capopaul/Jack-Bluetooth-Converter/doc/images_sw/bclk_oscilloscope.TIF

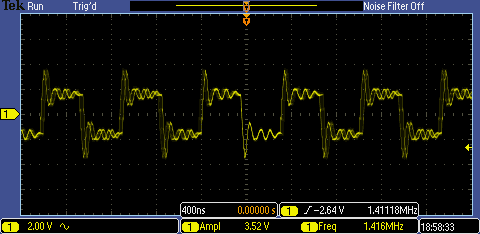
doc/images_sw/bclk_oscilloscope.TIF
