capopaul/Jack-Bluetooth-Converter/doc/images_sw/TEK00001.TIF

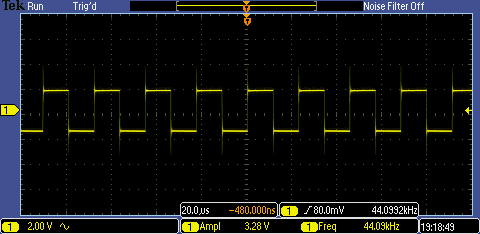
doc/images_sw/TEK00001.TIF
