capopaul/Jack-Bluetooth-Converter/doc/images_sw/TEK00002.TIF

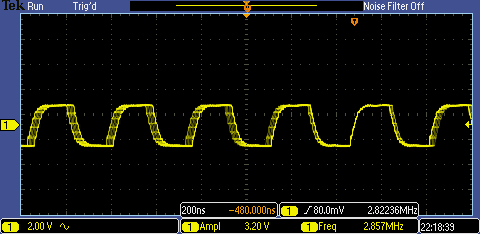
doc/images_sw/TEK00002.TIF
