capopaul/Jack-Bluetooth-Converter/doc/images_sw/TEK00003.TIF

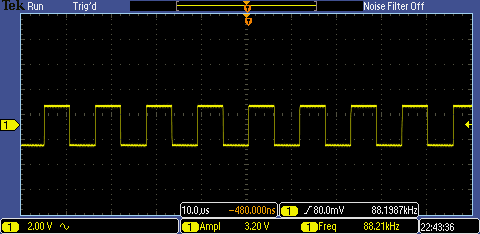
doc/images_sw/TEK00003.TIF
