capopaul/Jack-Bluetooth-Converter/doc/images_sw/TEK00004.TIF

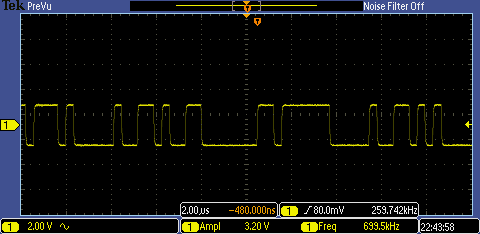
doc/images_sw/TEK00004.TIF
