capopaul/Jack-Bluetooth-Converter/doc/images_sw/TEK00005.TIF

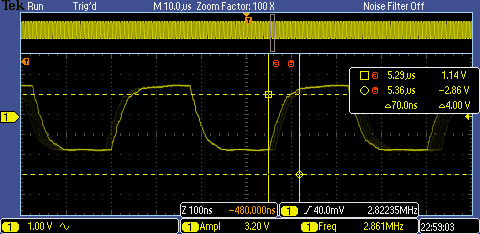
doc/images_sw/TEK00005.TIF
