capopaul/Jack-Bluetooth-Converter/doc/images_assembly/2025-04-11-PC-20250411_151901.jpg

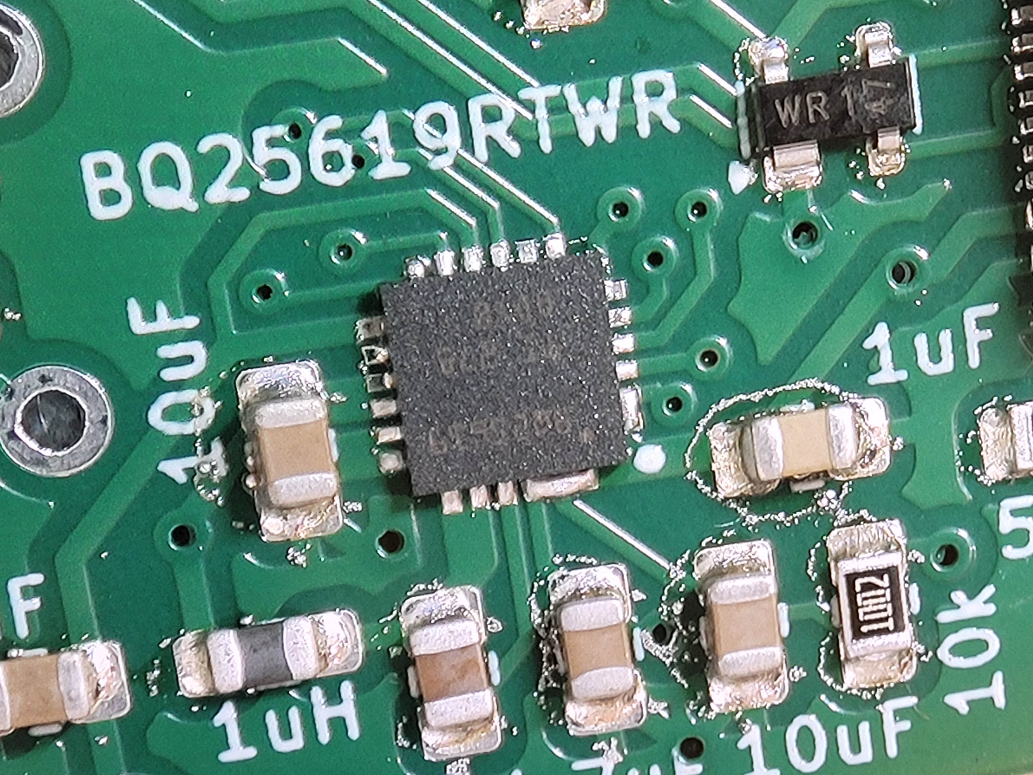
doc/images_assembly/2025-04-11-PC-20250411_151901.jpg
