capopaul/Jack-Bluetooth-Converter/doc/images_assembly/2025-04-20-PC-20250420_151838.jpg

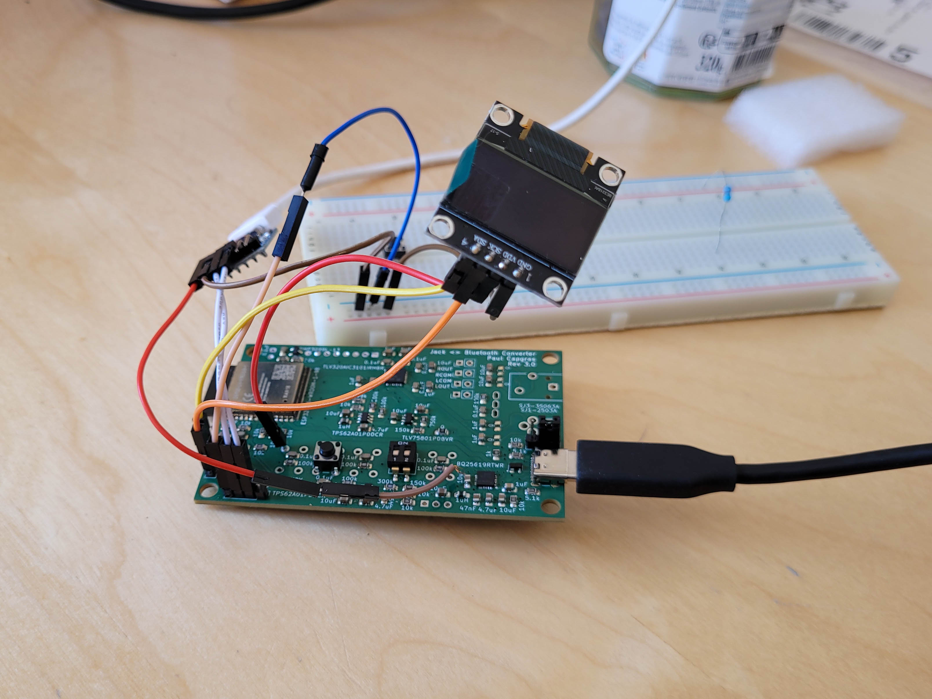
doc/images_assembly/2025-04-20-PC-20250420_151838.jpg
