capopaul/Jack-Bluetooth-Converter/doc/images_assembly/2025-06-28-PC-20250628_192159.jpg

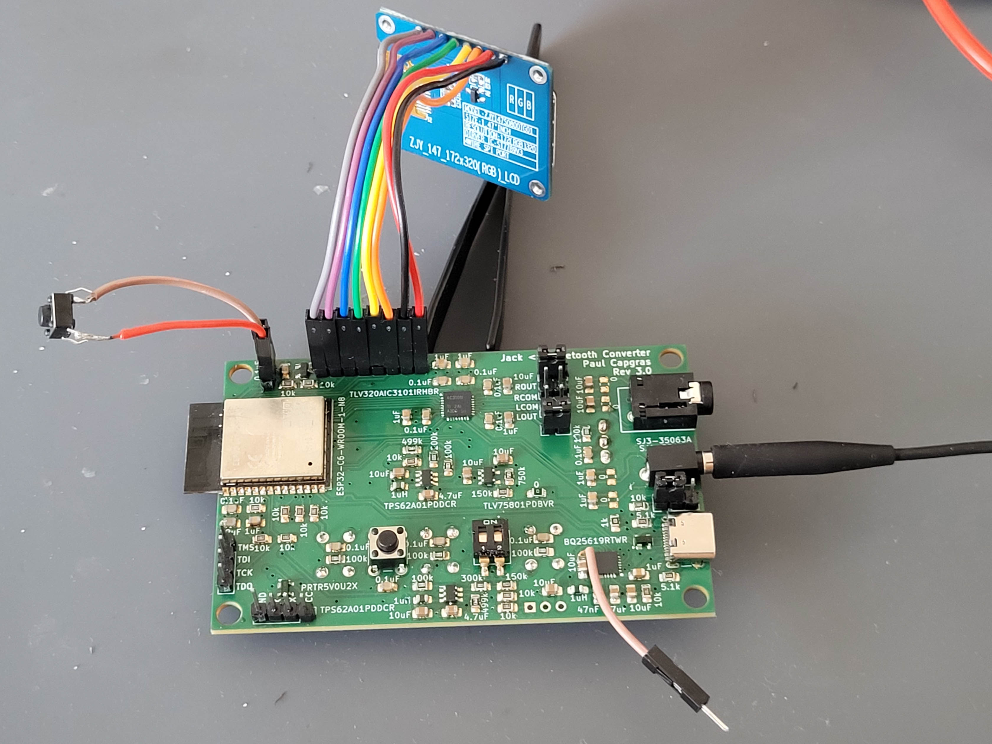
doc/images_assembly/2025-06-28-PC-20250628_192159.jpg
