capopaul/Jack-Bluetooth-Converter/doc/images_assembly/2025-07-02-PC-20250702_212738.jpg

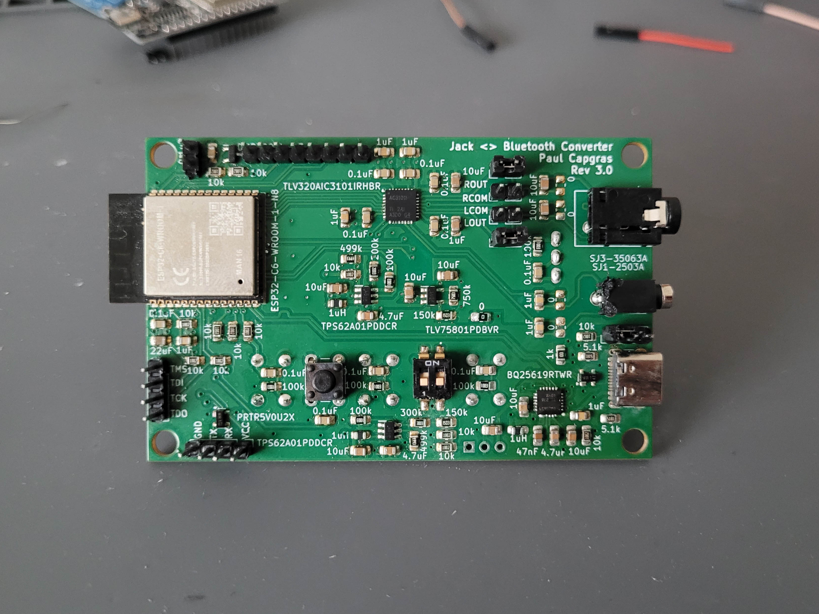
doc/images_assembly/2025-07-02-PC-20250702_212738.jpg
