capopaul/Jack-Bluetooth-Converter/software/jack2bluetooth/main/drivers/audio_codec.c

// Author : Paul Capgras
// Date   : Oct 6, 2025

// to configure and control GPIO pins
#include "driver/gpio.h"

#include "driver/i2c_master.h"
#include "i2c.h"
#include "esp_log.h"

#include "audio_codec.h"
#include "io_expander.h"

// Provides essential definitions for task management and delays
#include "freertos/FreeRTOS.h"

// Provide functions for task management and delays
#include "freertos/task.h"

#define REG7_DAC_MASK 0b00011110
#define REG7_FS_MASK 0x80

#define ADC_HPF_N0 0x7FE9
#define ADC_HPF_N1 0x8017
#define ADC_HPF_D1 0x7FD1

static uint8_t reg7_value = 0x00;

/********************************
 * EXTERNAL FUNCTION DECLARATIONS
 *******************************/

void audio_codec_reset(void)
{
    io_expander_clear(IO_EXPANDER_CODEC_RESET_L_MASK);
    vTaskDelay(pdMS_TO_TICKS(10));
    io_expander_set(IO_EXPANDER_CODEC_RESET_L_MASK);
    vTaskDelay(pdMS_TO_TICKS(10));
}

void audio_codec_sw_reset(void)
{
    // Register 1 - SW reset
    i2c_set(CODEC_ADDR, 1, 0x80);
}

void audio_codec_configure_pll(void)
{
    // Register 3 - PLL Programming Register A
    // D7   - 1    - PLL is enabled
    // D6-3 - 0000 - Q (ignored here)
    // D2-0 - 001  - P = 1
    i2c_set(CODEC_ADDR, 3, 0b10000001);
    is_expected(CODEC_TAG, 3, i2c_get(CODEC_ADDR, 3), 0b10000001);

    // Register 4 - PLL Programming Register B
    // D7-2 - 1000 00 - Set J to 32
    // D1-0 - 00      - Reserved
    i2c_set(CODEC_ADDR, 4, 0b10000000);
    is_expected(CODEC_TAG, 4, i2c_get(CODEC_ADDR, 4), 0b10000000);

    // Register 5 and 6
    // Set D to 0
    // MSB D7-0 (reg 5) 0
    // LSB D7-2 (reg 6) 0
    // D1-0             0
    // always write both, and in the order reg5 then reg6.
    is_expected(CODEC_TAG, 5, i2c_get(CODEC_ADDR, 5), 0b00000000);
    is_expected(CODEC_TAG, 6, i2c_get(CODEC_ADDR, 6), 0b00000000);

    // Register 11 - Audio Codec Overflow Flag Register
    // D7-4 - 0    - Ignore
    // D3-0 - 0001 - Set R to 1
    i2c_set(CODEC_ADDR, 11, 0b00000001);
    is_expected(CODEC_TAG, 11, i2c_get(CODEC_ADDR, 11), 0b00000001);

    // Register 101 - Clock register
    // D7-1 - 0
    // D0   - 0 - CODEC_CLKIN uses PLLDIV_OUT
    i2c_set(CODEC_ADDR, 101, 0b00000000);
    is_expected(CODEC_TAG, 101, i2c_get(CODEC_ADDR, 101), 0b00000000);

    // Register 102 - Clock Generation Control Register
    // D7-6 - 0    -
    // D5-4 - 10   - PLLCLK_IN uses BCLK
    // D3-0 - 0010 - Reserved
    i2c_set(CODEC_ADDR, 102, 0b00100010);
    is_expected(CODEC_TAG, 102, i2c_get(CODEC_ADDR, 102), 0b00100010);
}

void audio_codec_configure_i2s_settings(codec_fs_t fs)
{
    // Register 2 - default is good
    // Register 8 - default is good
    // Register 9 - default is good
    // Register 10 - default is good

    switch (fs)
    {
    case FS_44_1HZ:

        // Register 7 - Codec Data-Path Setup Register
        // D7   - 1  - Set fs=44.1kHz
        reg7_value = reg7_value | REG7_FS_MASK;

        i2c_set(CODEC_ADDR, 7, reg7_value);
        is_expected(CODEC_TAG, 7, i2c_get(CODEC_ADDR, 7), reg7_value);
        break;

    default:
        ESP_LOGE(CODEC_TAG, "Unsupported fs");
        break;
    }
}

void audio_codec_connect_input_to_dac()
{

    // Register 7 - Codec Data-Path Setup Register
    // D4-3 - 01 - Left DAC plays left input data
    // D2-1 - 01 - Right DAC plays right input data
    reg7_value = (reg7_value & ~REG7_DAC_MASK) | 0b00001010;
    i2c_set(CODEC_ADDR, 7, reg7_value);
    is_expected(CODEC_TAG, 7, i2c_get(CODEC_ADDR, 7), reg7_value);

    // Register 41 - DAC Output Switching Control Register
    // D7-6 - 10 - Left DAC output selects DAC-L2 path to left high power output drivers
    // D5-4 - 10 - Right DAC output selects DAC-R2 path to right high power output drivers
    // D3-0 - 0000
    i2c_set(CODEC_ADDR, 41, 0b10100000);
    is_expected(CODEC_TAG, 41, i2c_get(CODEC_ADDR, 41), 0b10100000);
}

void audio_codec_connect_line2_to_adc()
{
    // Register 17 - MIC2L/R to Left-ADC Control Register
    // D7-4 - 0000 - Connect LINE2L to left-ADC PGA - Input level control gain = 0 dB
    // D3-0 - 1111 - LINE2R is not connected to the left-ADC PGA
    // 0000 1111
    i2c_set(CODEC_ADDR, 17, 0b00001111);
    is_expected(CODEC_TAG, 17, i2c_get(CODEC_ADDR, 17), 0b00001111);

    // Register 18 - MIC2/LINE2 to Right-ADC Control Register
    // D7-4 - 1111 - LINE2L is not connected to the right-ADC PGA
    // D3-0 - 0000 - Connect LINE2R to right-ADC PGA - Input level control gain = 0 dB
    // 1111 0000
    i2c_set(CODEC_ADDR, 18, 0b11110000);
    is_expected(CODEC_TAG, 18, i2c_get(CODEC_ADDR, 18), 0b11110000);
}

static void audio_codec_write_coefficient(uint8_t msb_register, uint16_t coefficient)
{
    uint8_t msb = (uint8_t)(coefficient >> 8);
    uint8_t lsb = (uint8_t)coefficient;

    i2c_set(CODEC_ADDR, msb_register, msb);
    is_expected(CODEC_TAG, msb_register,
                i2c_get(CODEC_ADDR, msb_register), msb);
    i2c_set(CODEC_ADDR, msb_register + 1, lsb);
    is_expected(CODEC_TAG, msb_register + 1,
                i2c_get(CODEC_ADDR, msb_register + 1), lsb);
}

void audio_codec_configure_adc_high_pass(void)
{
    /* First-order 10 Hz HPF at fs=44.1 kHz:
     * H(z) = N0 * (1 - z^-1) / (32768 - D1 * z^-1)
     * Coefficients use the codec's signed 16-bit format. The gain is
     * normalized at Nyquist, so the passband remains at approximately 0 dB.
     */

    // Page 1 contains the programmable ADC HPF coefficients.
    i2c_set(CODEC_ADDR, 0, 1);
    is_expected(CODEC_TAG, 0, i2c_get(CODEC_ADDR, 0), 1);

    // Left ADC: N0 (65-66), N1 (67-68), D1 (69-70).
    audio_codec_write_coefficient(65, ADC_HPF_N0);
    audio_codec_write_coefficient(67, ADC_HPF_N1);
    audio_codec_write_coefficient(69, ADC_HPF_D1);

    // Right ADC: N0 (71-72), N1 (73-74), D1 (75-76).
    audio_codec_write_coefficient(71, ADC_HPF_N0);
    audio_codec_write_coefficient(73, ADC_HPF_N1);
    audio_codec_write_coefficient(75, ADC_HPF_D1);

    // Return to page 0 before accessing the normal control registers.
    i2c_set(CODEC_ADDR, 0, 0);
    is_expected(CODEC_TAG, 0, i2c_get(CODEC_ADDR, 0), 0);

    // Register 107 D7/D6: use programmable coefficients on both ADCs.
    uint8_t reg107 = i2c_get(CODEC_ADDR, 107) & 0x0c;
    reg107 |= 0xc0;
    i2c_set(CODEC_ADDR, 107, reg107);
    is_expected(CODEC_TAG, 107, i2c_get(CODEC_ADDR, 107), reg107);

    // Register 12 D7-D6/D5-D4 = 01: enable left/right ADC HPFs.
    // When register 107 selects programmable coefficients, the nonzero
    // setting enables the custom filter rather than the built-in 198 Hz HPF.
    uint8_t reg12 = (i2c_get(CODEC_ADDR, 12) & 0x0f) | 0x50;
    i2c_set(CODEC_ADDR, 12, reg12);
    is_expected(CODEC_TAG, 12, i2c_get(CODEC_ADDR, 12), reg12);
}

void audio_codec_configure_sink_topology()
{
    // Register 14 - Headset/Button Press Detection Register B
    // D7   - 1 - Programs HPout for AC-coupled
    // D6-0 -   - ignore
    i2c_set(CODEC_ADDR, 14, 0b10000000);

    // Register 40 - default is good
    // Register 42 - default is good

    // Register 38 - Headset/Button Press Detection Register B
    // D7-6 - 00   - reserved
    // D5-3 - 010  - HPRCOM is configured as independent single-ended output
    // D2-1 - 00   - ignored
    // D0   - 0    - reserved
    i2c_set(CODEC_ADDR, 38, 0b00010000);
    is_expected(CODEC_TAG, 38, i2c_get(CODEC_ADDR, 38), 0b00010000);
}

void audio_codec_power_up_adc(void)
{
    // Register 19 - Power up Left-ADC
    // D7   - 0
    // D6-3 - 1111
    // D2   - 1    - Left-ADC channel is powered up
    // D1-0 - 00
    // 0111 1100
    i2c_set(CODEC_ADDR, 19, 0b01111100);
    is_expected(CODEC_TAG, 19, i2c_get(CODEC_ADDR, 19), 0b01111100);

    // Register 22 - Power up right-ADC
    // D7   - 0
    // D6-3 - 1111
    // D2   - 1    - Right-ADC channel is powered up
    // D1-0 - 00
    // 0111 1100
    i2c_set(CODEC_ADDR, 22, 0b01111100);
    is_expected(CODEC_TAG, 22, i2c_get(CODEC_ADDR, 22), 0b01111100);
}

void audio_codec_power_up_dac(void)
{
    // Register 37 - DAC Power and Output Driver Control Register
    // D7   - 1 - Left DAC is powered up
    // D6   - 1 - Right DAC is powered up
    // D5-0 - 0
    // Write 1100 0000
    i2c_set(CODEC_ADDR, 37, 0b11000000);
    is_expected(CODEC_TAG, 37, i2c_get(CODEC_ADDR, 37), 0b11000000);
}

void audio_codec_power_up_headphone(void)
{
    // Register 51 - HPLout output level control register
    // D7-4 - 0000
    // D3   - 0 - mute
    // D2   - 1
    // D1   - 1
    // D0   - 1 - Power up
    i2c_set(CODEC_ADDR, 51, 0b00000111);

    // Register 65 - HPRout output level control register
    // D7-4 - 0000
    // D3   - 0 - mute
    // D2   - 1
    // D1   - 1
    // D0   - 1 - Power up
    i2c_set(CODEC_ADDR, 65, 0b00000111);
}

void audio_codec_mute_adc(void)
{
    // Set D7 in both ADC PGA gain registers, preserving D6-0 (gain).
    uint8_t left = i2c_get(CODEC_ADDR, 15) | 0x80;
    uint8_t right = i2c_get(CODEC_ADDR, 16) | 0x80;
    i2c_set(CODEC_ADDR, 15, left);
    is_expected(CODEC_TAG, 15, i2c_get(CODEC_ADDR, 15), left);
    i2c_set(CODEC_ADDR, 16, right);
    is_expected(CODEC_TAG, 16, i2c_get(CODEC_ADDR, 16), right);
}

void audio_codec_unmute_adc()
{
    // Register 15 - Left-ADC PGA Gain Control Register
    // D7   - 0 - The left-ADC PGA is not muted.
    // D6-0 - 0
    i2c_set(CODEC_ADDR, 15, 0b00000000);
    is_expected(CODEC_TAG, 15, i2c_get(CODEC_ADDR, 15), 0b00000000);

    // Register 16 - Right-ADC PGA Gain Control Register
    // D7   - 0 - The right-ADC PGA is not muted.
    // D6-0 - 0
    i2c_set(CODEC_ADDR, 16, 0b00000000);
    is_expected(CODEC_TAG, 16, i2c_get(CODEC_ADDR, 16), 0b00000000);
}

void audio_codec_unmute_dac(void)
{
    // Register 43 - Left-DAC Digital Volume Control Register
    // D7   - 0 - Unmute left-DAC channel
    // D6-0 - 0
    i2c_set(CODEC_ADDR, 43, 0b00000000);
    is_expected(CODEC_TAG, 43, i2c_get(CODEC_ADDR, 43), 0b00000000);

    // Register 44 - Right-DAC Digital Volume Control Register
    // D7   - 0 - Unmute right-DAC channel
    // D6-0 - 0
    i2c_set(CODEC_ADDR, 44, 0b00000000);
    is_expected(CODEC_TAG, 44, i2c_get(CODEC_ADDR, 44), 0b00000000);
}

void audio_codec_unmute_headphone()
{
    // Register 51 - HPLout output level control register
    // D7-4 - 0000
    // D3   - 1 - Unmute
    // D2   - 1
    // D1   - 1
    // D0   - 1 - Power up
    i2c_set(CODEC_ADDR, 51, 0b00001111);

    // Register 65 - HPRout output level control register
    // D7-4 - 0000
    // D3   - 1 - Unmute
    // D2   - 1
    // D1   - 1
    // D0   - 1 - Power up
    i2c_set(CODEC_ADDR, 65, 0b00001111);
}

void audio_codec_check_power_ready(void)
{
    uint8_t status = 0;
    for (int attempt = 0; attempt < 50; ++attempt)
    {
        vTaskDelay(pdMS_TO_TICKS(10));
        status = i2c_get(0x18, 94);
        // 0xff is also the current I2C helper's error return.
        if (status != 0xff && (status & 0xc6) == 0xc6)
        {
            ESP_LOGI("AUDIO_CODEC", "DACs and headphone outputs powered up");
            return;
        }
    }
    ESP_LOGW("AUDIO_CODEC", "Power readiness timed out: register 94 = 0x%02x", status);
}
