capopaul/Jack-Bluetooth-Converter/software/jack2bluetooth/main/drivers/audio_codec.h

// Author : Paul Capgras
// Date   : Oct 6, 2025
#pragma once

#include "io_expander.h"

#define CODEC_ADDR 0x18
#define CODEC_TAG "AUDIO_CODEC"

typedef enum
{
    FS_44_1HZ
} codec_fs_t;

/********************************
 * EXTERNAL FUNCTION DECLARATIONS
 *******************************/

// HW Codec reset uses I2C through the initialized IO expander.
void audio_codec_reset(void);

// SW Codec reset using codec registers
void audio_codec_sw_reset(void);

// Configure the required PLL registers
void audio_codec_configure_pll(void);

void audio_codec_configure_i2s_settings(codec_fs_t fs);

void audio_codec_connect_input_to_dac(void);

void audio_codec_connect_line2_to_adc(void);

// Enable the ADCs' programmable first-order 10 Hz high-pass filters.
void audio_codec_configure_adc_high_pass(void);

void audio_codec_configure_sink_topology(void);

void audio_codec_power_up_adc(void);

void audio_codec_power_up_dac(void);

void audio_codec_power_up_headphone(void);

void audio_codec_mute_adc(void);

void audio_codec_unmute_adc(void);

void audio_codec_unmute_dac(void);

void audio_codec_unmute_headphone();

// Poll power readiness after the I2S clock has started (up to 500 ms).
void audio_codec_check_power_ready(void);
