capopaul/Jack-Bluetooth-Converter/software/jack2bluetooth/main/drivers/bt_app_a2dp_source.h

#pragma once

#include "esp_err.h"

/********************************
 * EXTERNAL FUNCTION DECLARATIONS
 *******************************/

/**
 * @brief Start the A2DP source application after Bluedroid is enabled.
 *
 * This starts the Bluetooth application task and schedules initialization of
 * GAP discovery, AVRCP, A2DP, stream endpoints, and the media state machine.
 */
void bt_app_a2dp_source_start(void);
