capopaul/Jack-Bluetooth-Converter/software/jack2bluetooth/main/drivers/i2c.h

// Author : Paul Capgras
// Date   : Oct 10, 2025
#pragma once

#define I2C_GPIO_SDA 21
#define I2C_GPIO_SCL 19

void i2c_init();

// Set an i2c register
int i2c_set(int chip_address, int register_address, uint8_t data);

// Read an i2c register
uint8_t i2c_get(int chip_address, int register_address);

// Log an error under the caller's tag when a register differs from its expected value.
int is_expected(const char *tag, int register_address, uint8_t read_value, uint8_t expected_value);

int i2c_detect();
int i2c_dump(int chip_addr, int size);
