capopaul/Jack-Bluetooth-Converter/software/jack2bluetooth/main/drivers/bt_app_core.h

/*
 * SPDX-FileCopyrightText: 2026 Espressif Systems (Shanghai) CO LTD
 *
 * SPDX-License-Identifier: Unlicense OR CC0-1.0
 */
#pragma once

#include <stdint.h>
#include <stdbool.h>
#include <stdio.h>

/* log tag */
#define BT_APP_CORE_TAG "BT_APP_CORE"

/**
 * @brief    handler for the dispatched work
 *
 * @param [in] event  message event id
 * @param [in] param  pointer to the parameter
 */
typedef void (*bt_app_cb_t)(uint16_t event, void *param);

/**
 * @brief    parameter deep-free function
 *
 * @param [in] p_param  pointer to the parameter
 */
typedef void (*bt_app_free_cb_t)(void *p_param);

typedef enum
{
    BT_APP_SIG_WORK_DISPATCH = 0x01,
} bt_app_sig_t;

/* message to be sent */
typedef struct
{
    bt_app_sig_t sig;         /*!< signal to bt_app_task */
    uint16_t event;           /*!< message event id */
    bt_app_cb_t cb;           /*!< context switch callback */
    bt_app_free_cb_t free_cb; /*!< parameter deep-free function */
    void *param;              /*!< parameter area needs to be last */
} bt_app_msg_t;

/**
 * @brief    parameter deep-copy function to be customized
 *
 * @param [in] p_dest  pointer to the destination
 * @param [in] p_src   pointer to the source
 * @param [in] len     data length in byte
 */
typedef void (*bt_app_copy_cb_t)(void *p_dest, void *p_src, int len);

/********************************
 * EXTERNAL FUNCTION DECLARATIONS
 *******************************/

void bt_app_init(void);
void bt_app_task_shut_down(void);

bool bt_app_work_dispatch(bt_app_cb_t p_cback, uint16_t event, void *p_params, int param_len,
                          bt_app_copy_cb_t p_copy_cback, bt_app_free_cb_t p_free_cback);
