capopaul/Jack-Bluetooth-Converter/software/esp32_i2c/main/cmd_i2ctools.h

/*
 * SPDX-FileCopyrightText: 2022-2024 Espressif Systems (Shanghai) CO LTD
 *
 * SPDX-License-Identifier: Apache-2.0
 */

void register_i2ctools(void);

extern i2c_master_bus_handle_t tool_bus_handle;
